sanmaneric/PedalSynth/Diagrams/chorusbreadboard.rev0.jpg

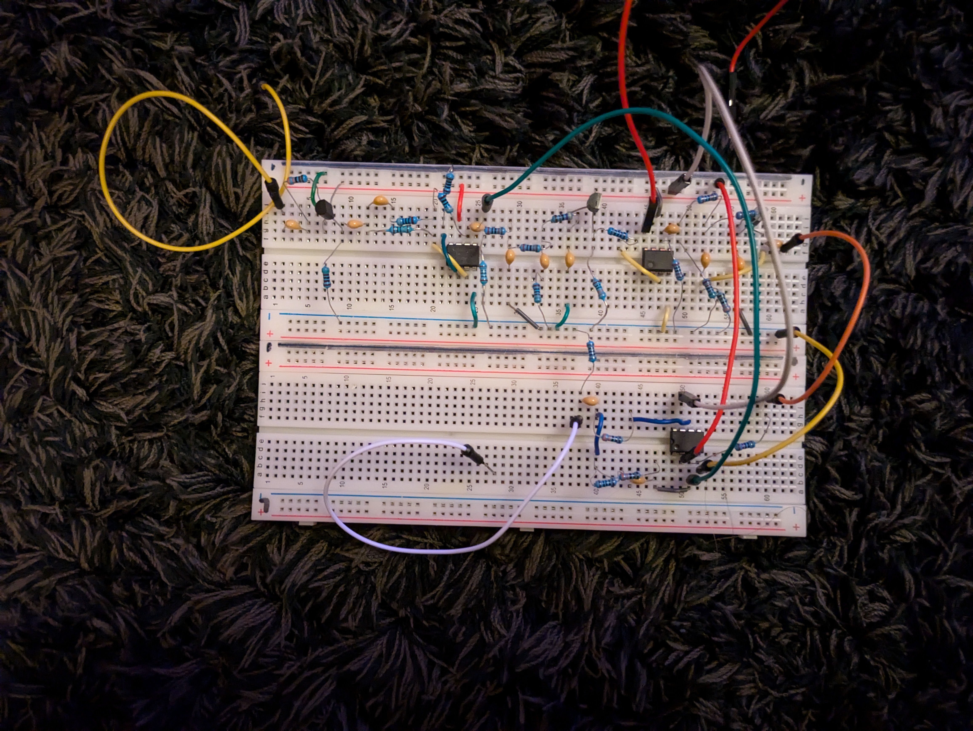
Diagrams/chorusbreadboard.rev0.jpg
