sanmaneric/PedalSynth/Diagrams/Level 0 Diagram.drawio-rev0.png

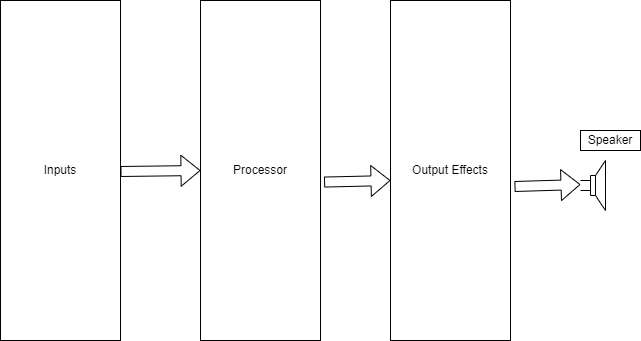
Diagrams/Level 0 Diagram.drawio-rev0.png
