sanmaneric/PedalSynth/Diagrams/Level 1 Diagram.drawio-rev1.png

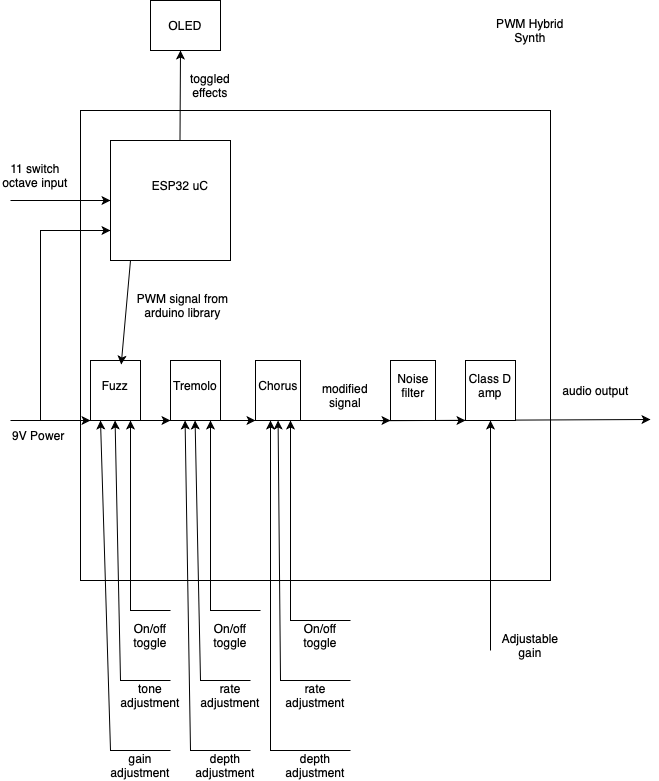
Diagrams/Level 1 Diagram.drawio-rev1.png
