sanmaneric/PedalSynth/Weekly Progress Reports/Progresss Photos/oled-test-14Nov.JPG

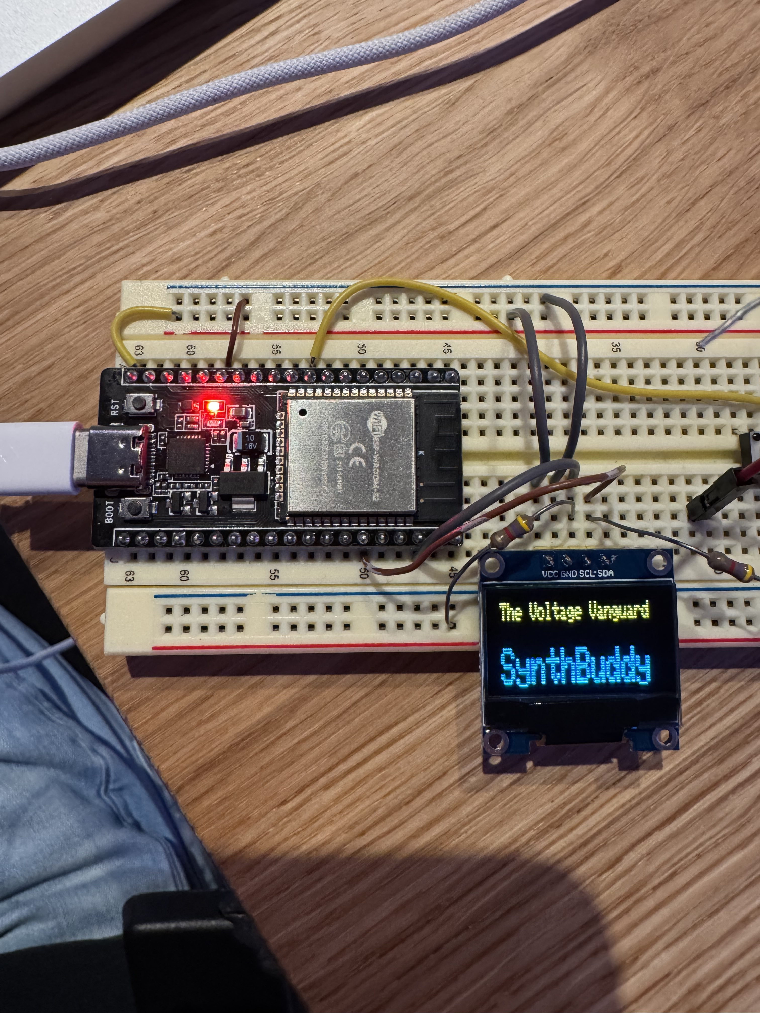
Weekly Progress Reports/Progresss Photos/oled-test-14Nov.JPG
