sanmaneric/PedalSynth/Electrical Design/Docs/Combined Design Package/PedalSynth-Pkg-7Nov.pdf

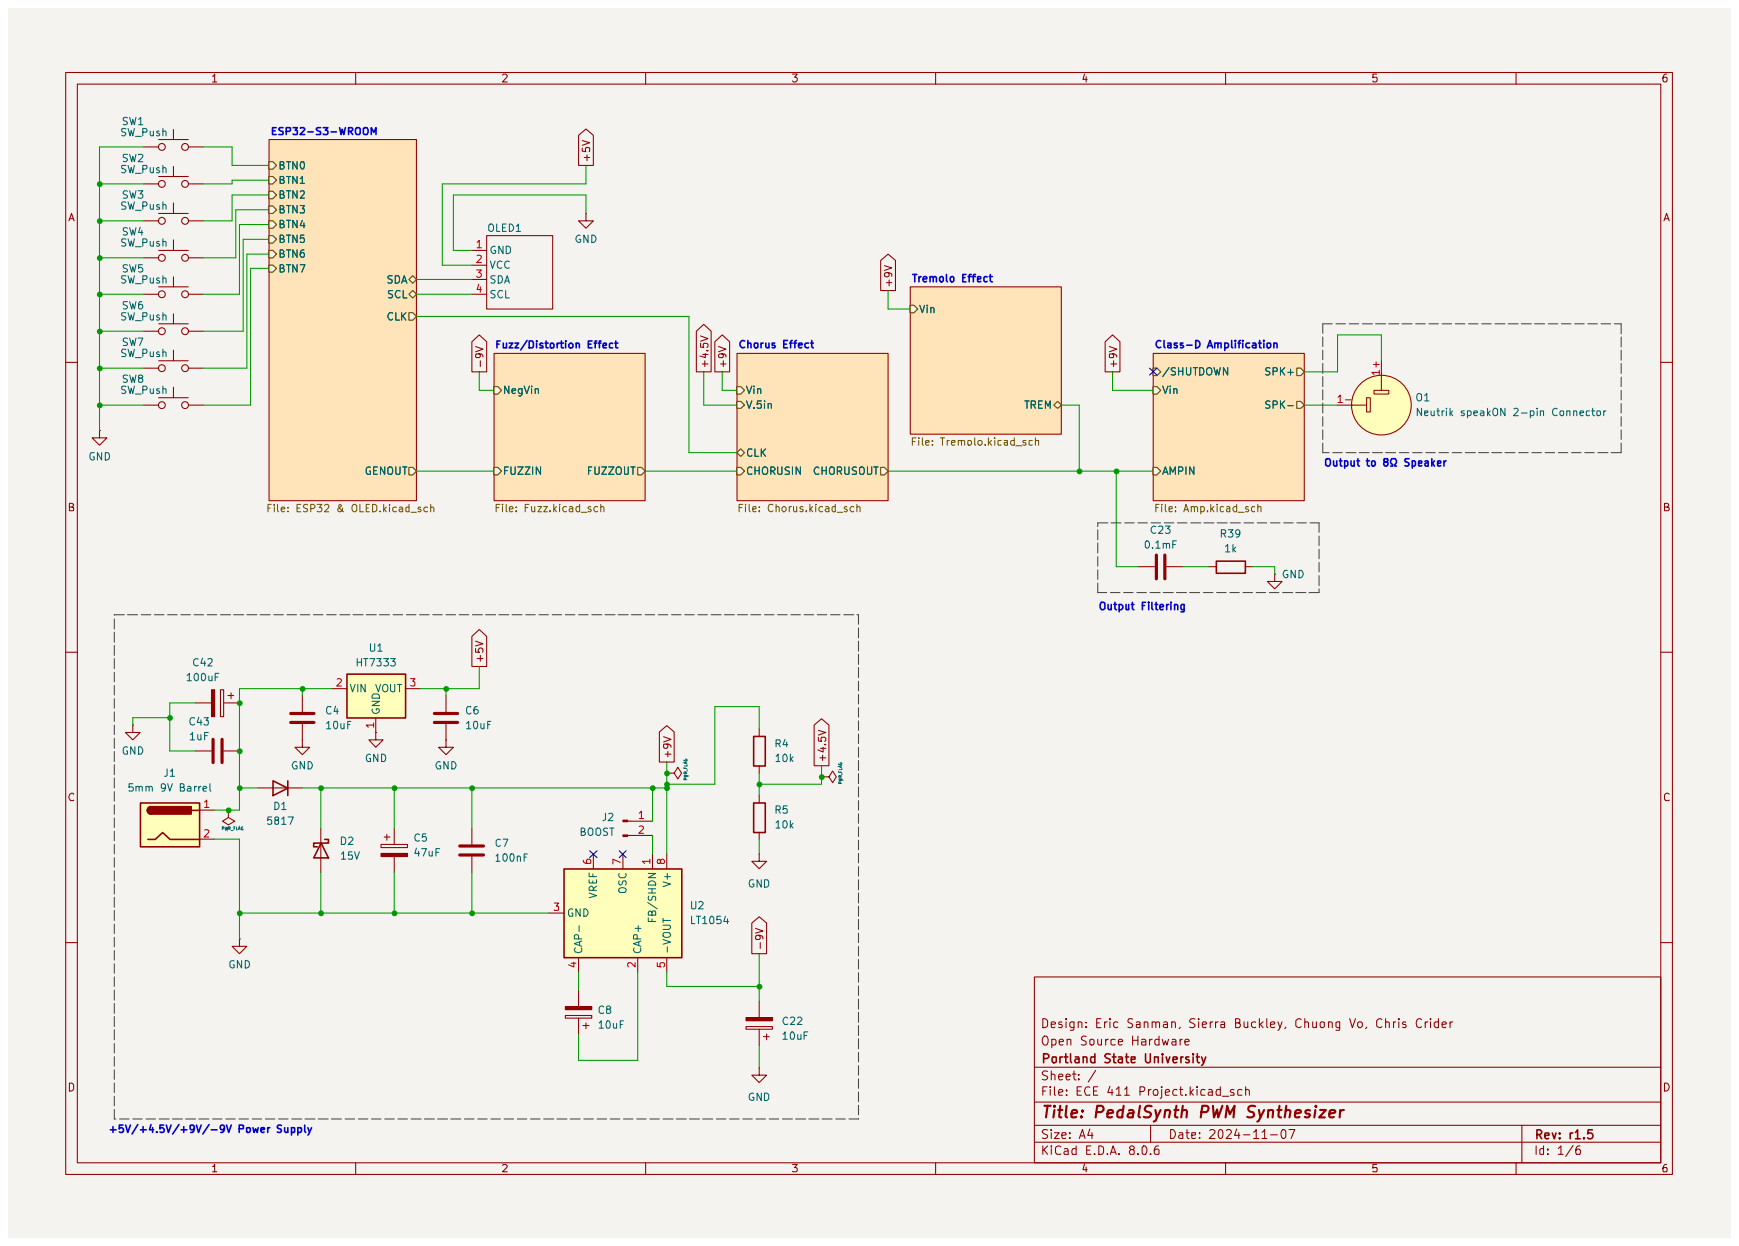
[picture p41: page 1]

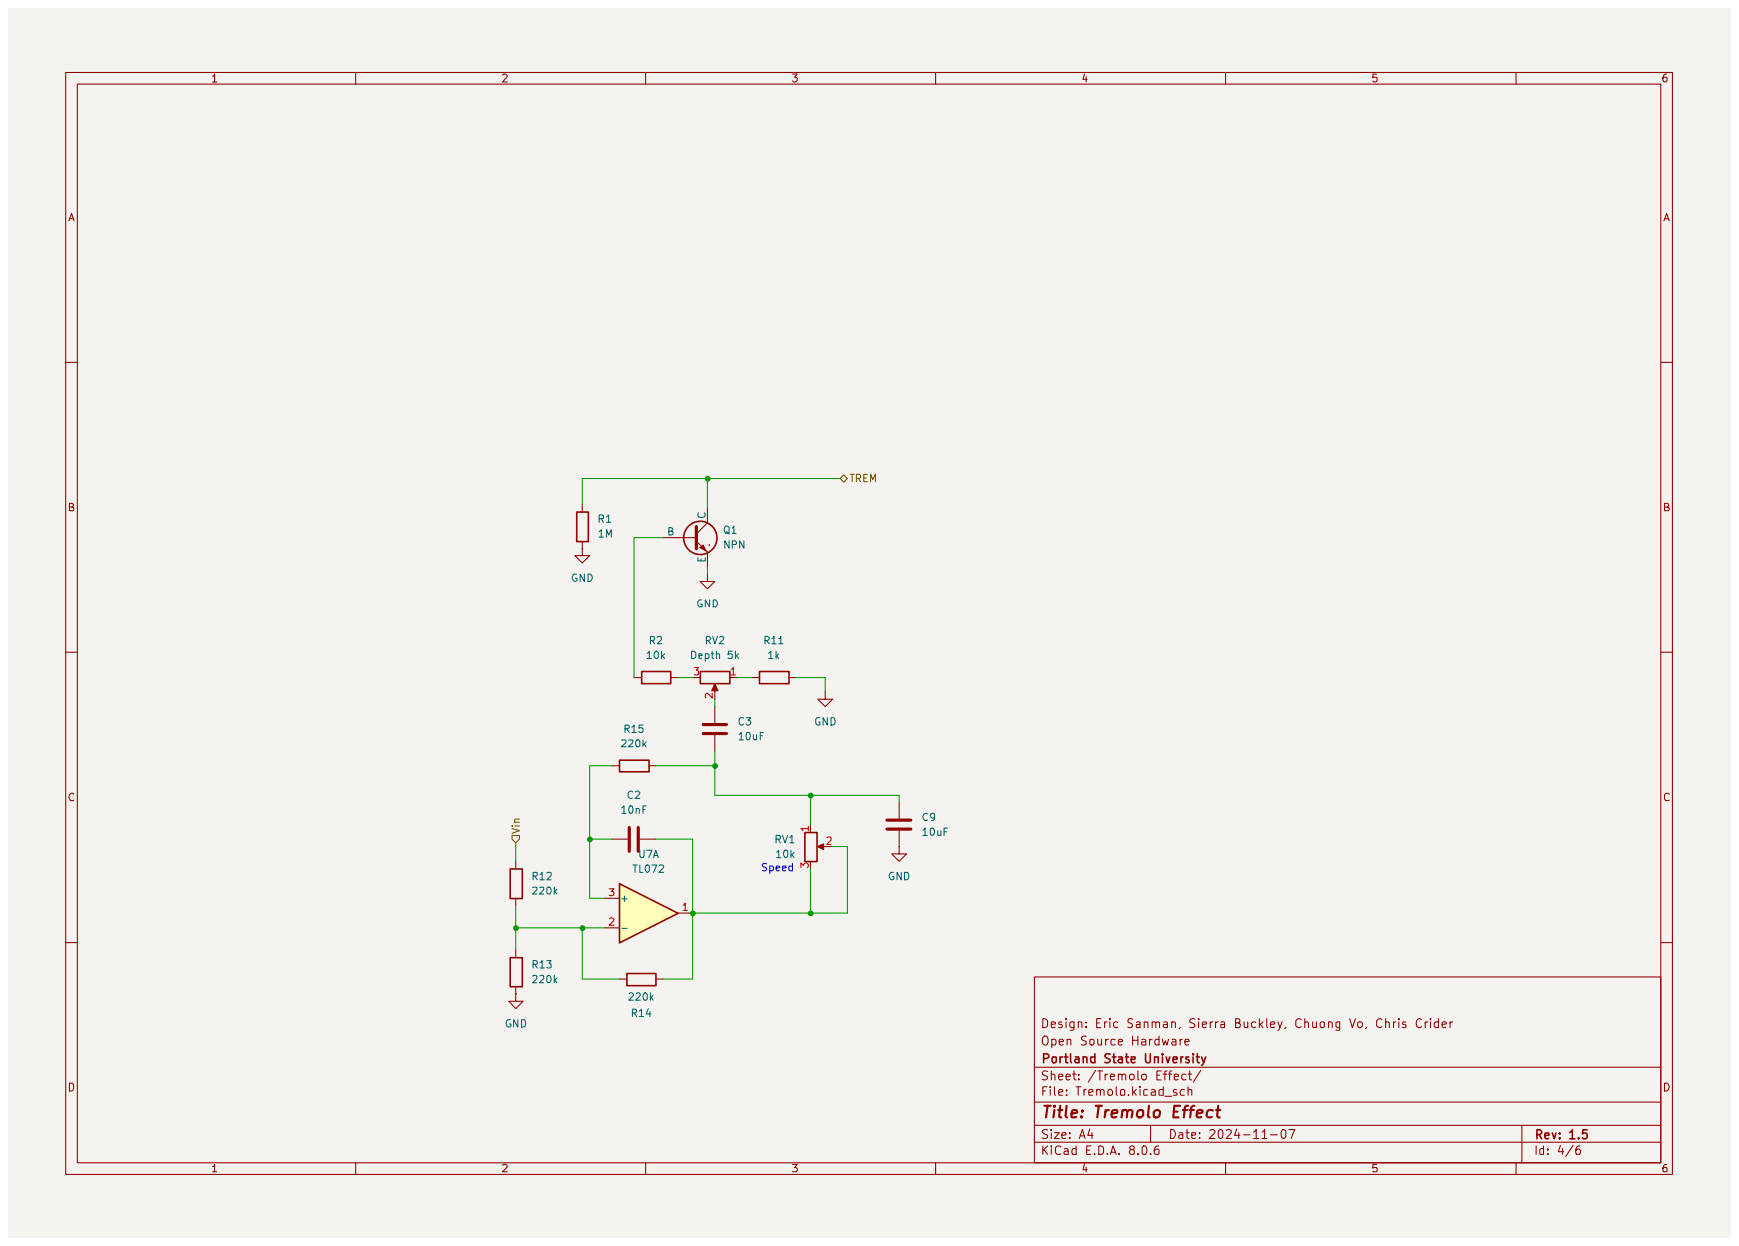
[picture p42: page 2]

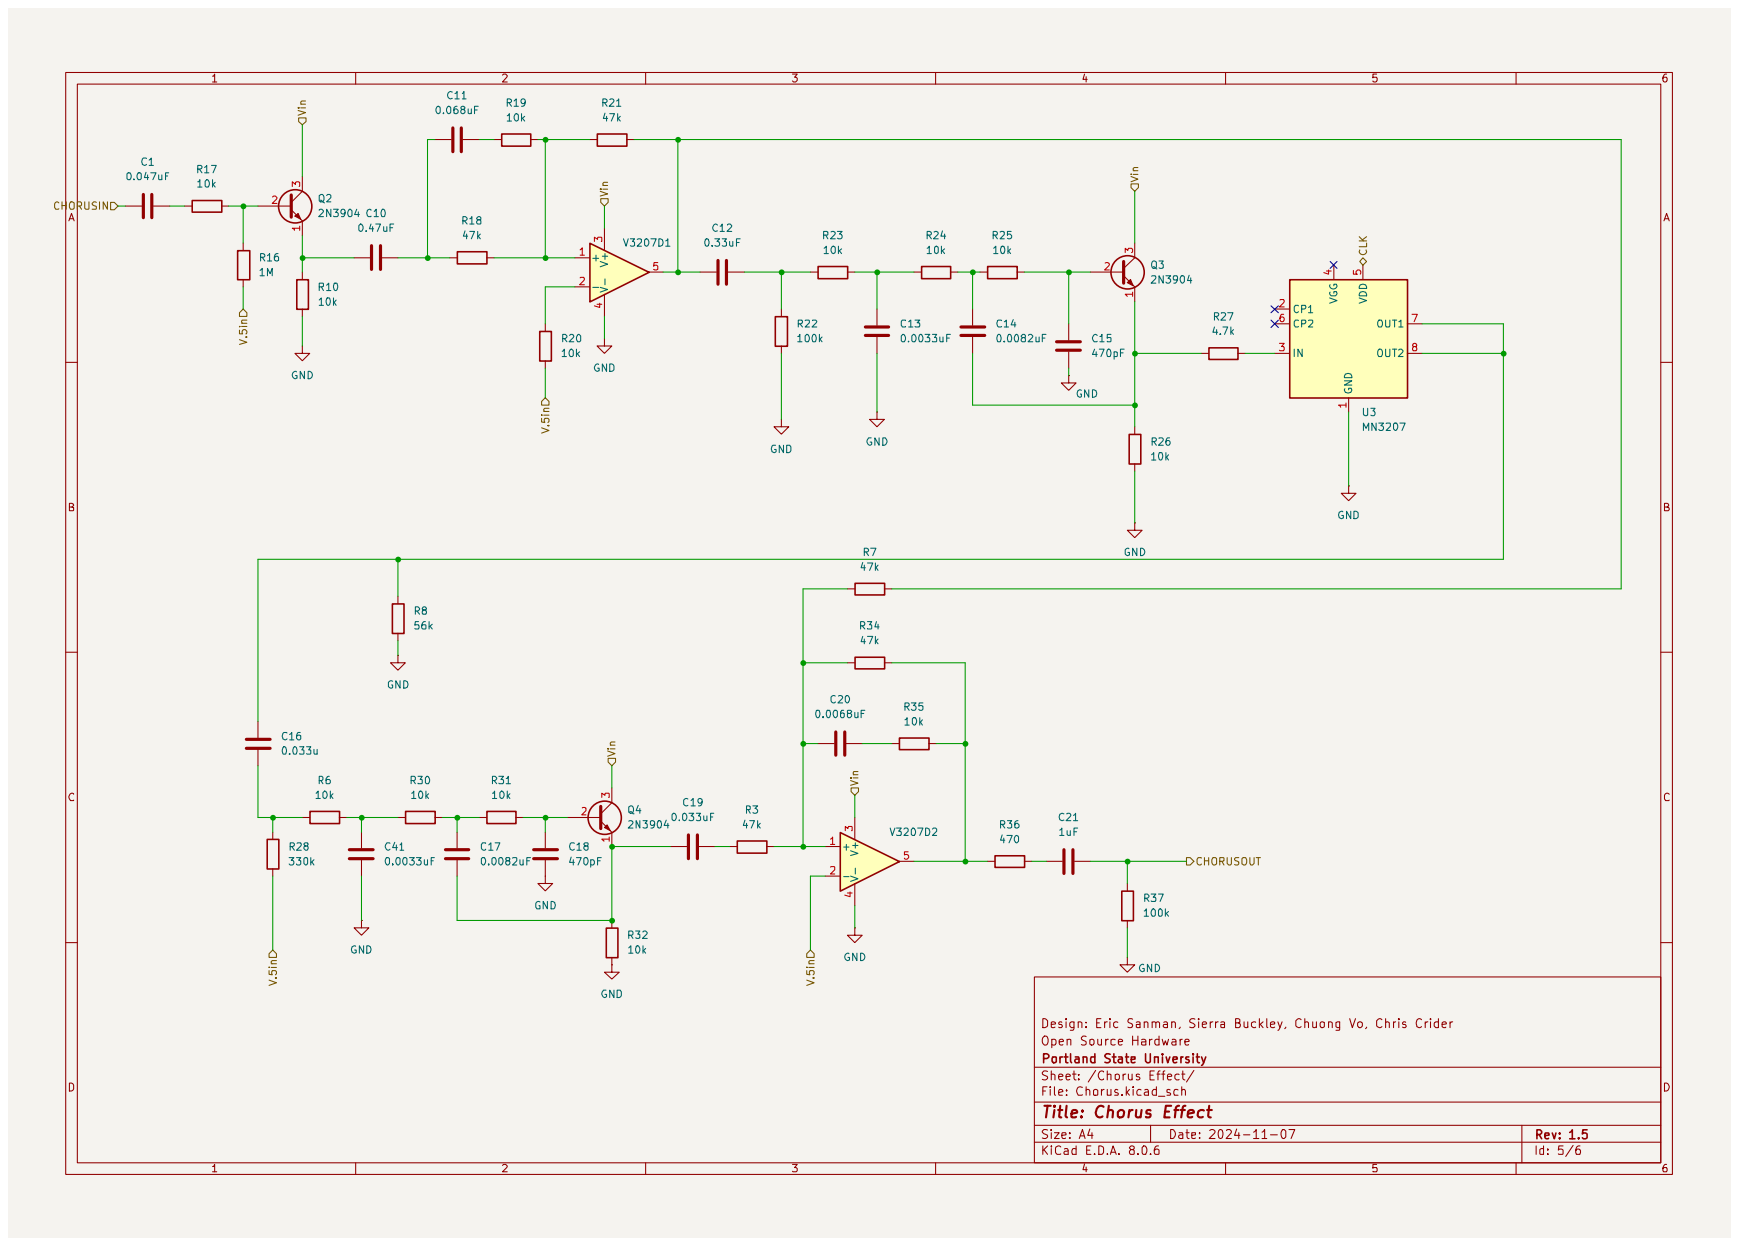
[picture p43: page 3]

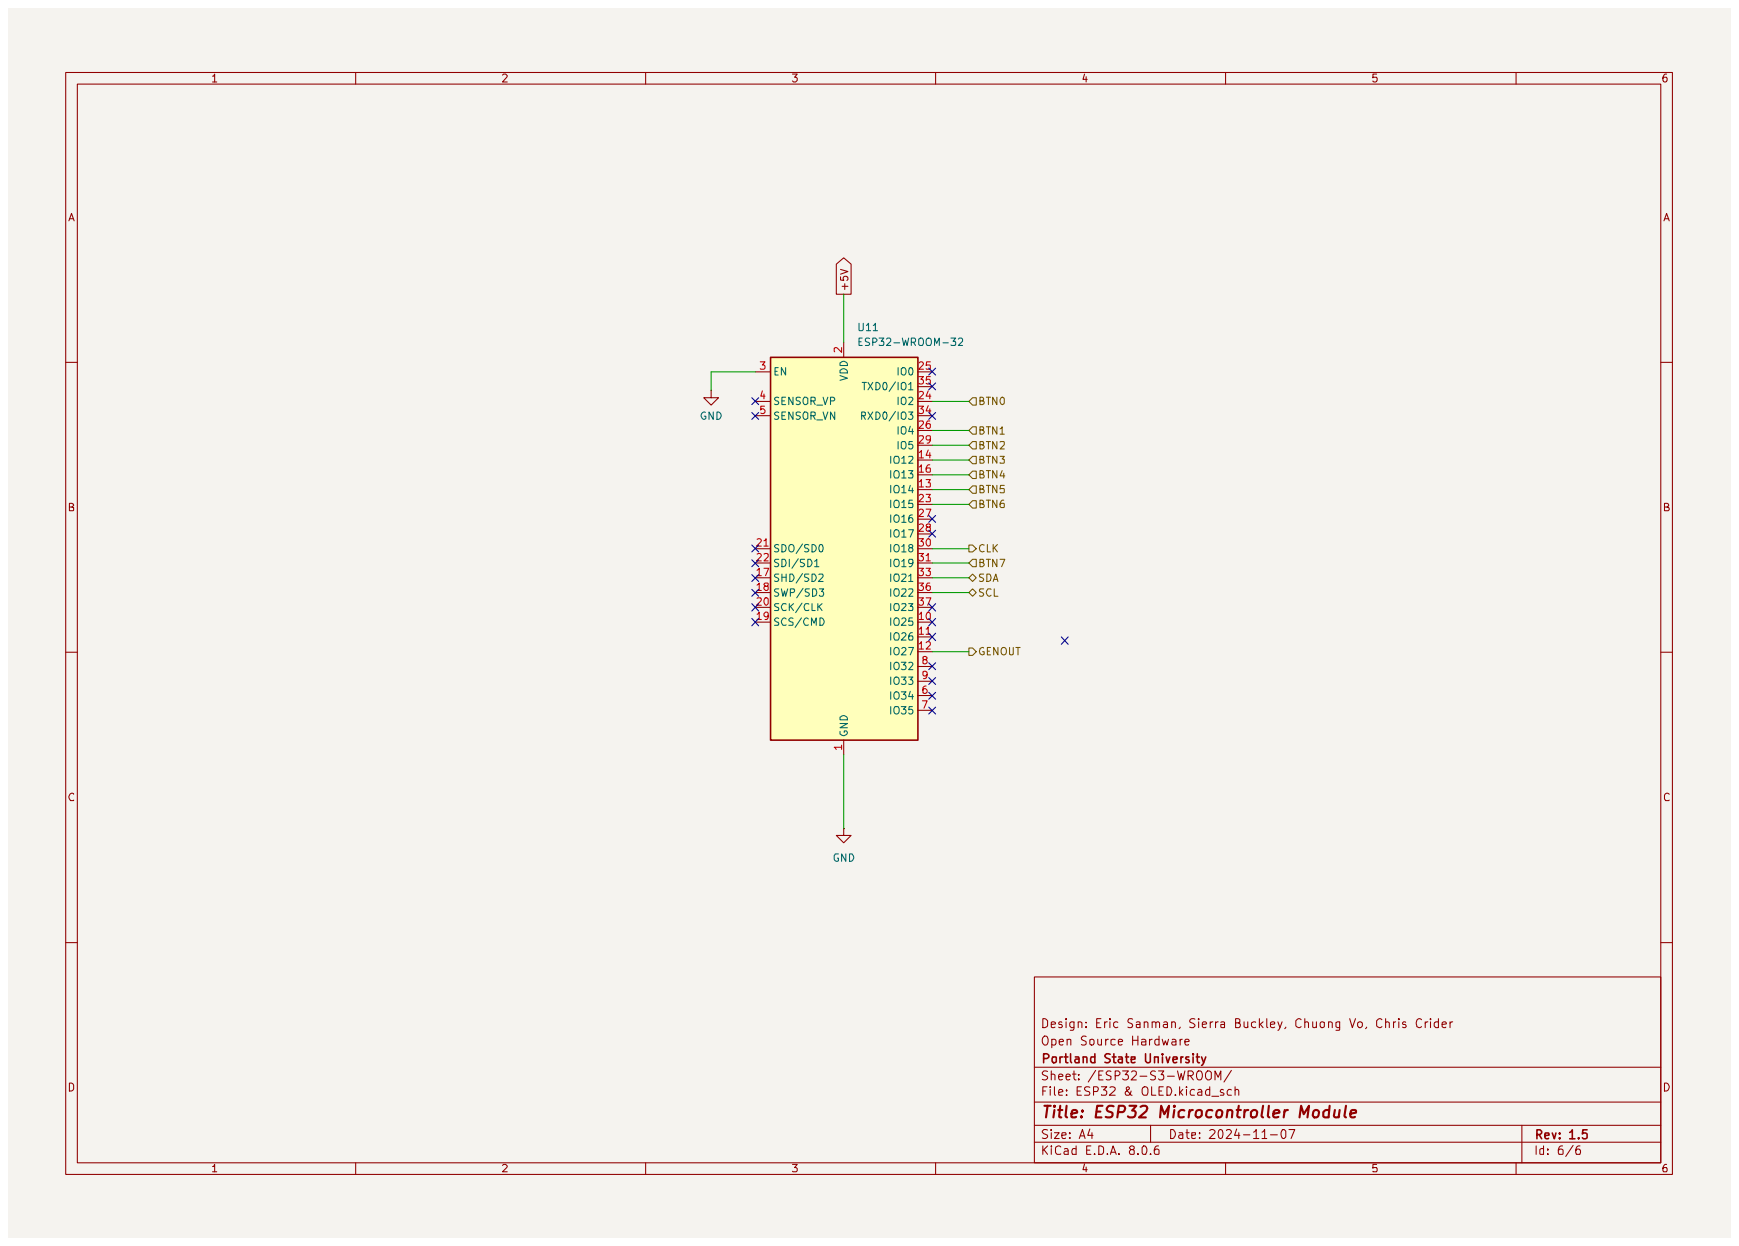
[picture p44: page 4]

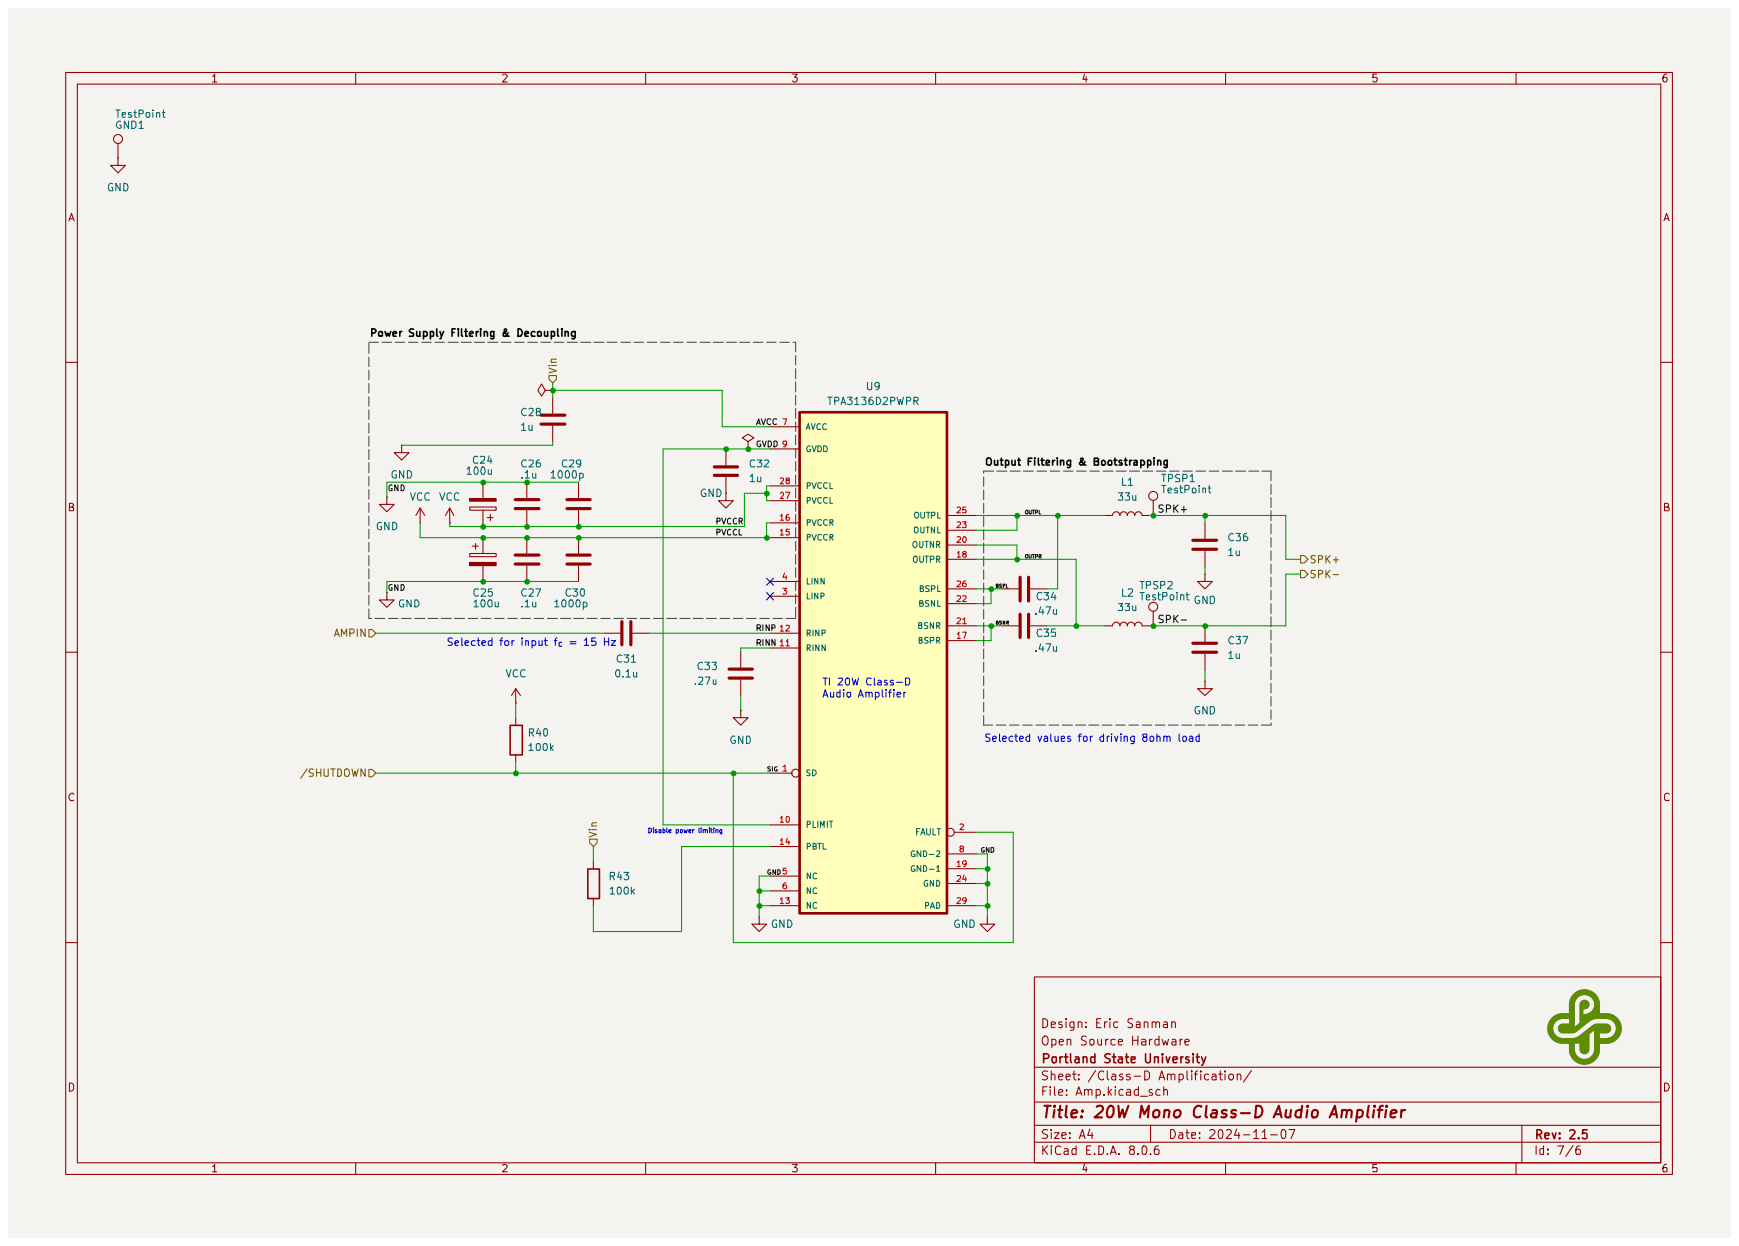
[picture p45: page 5]

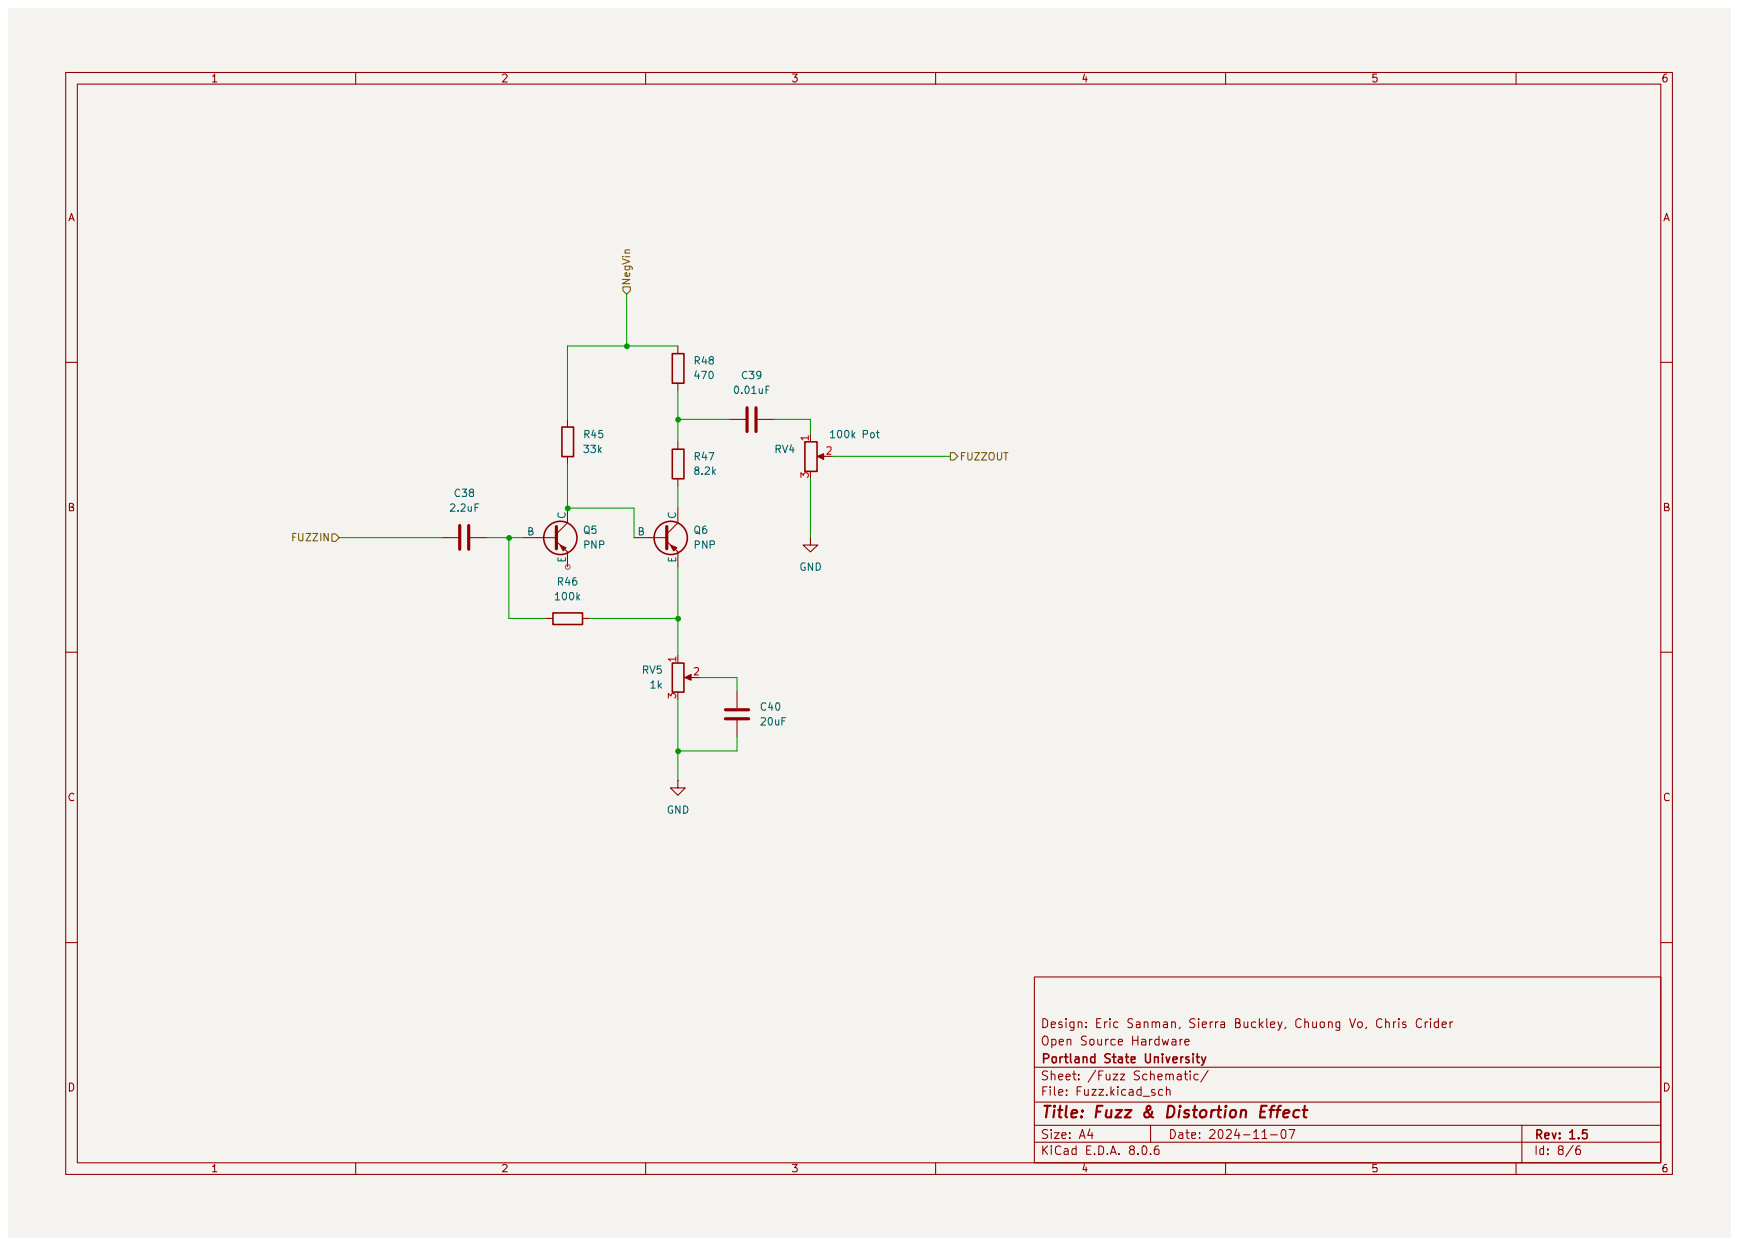
[picture p46: page 6]

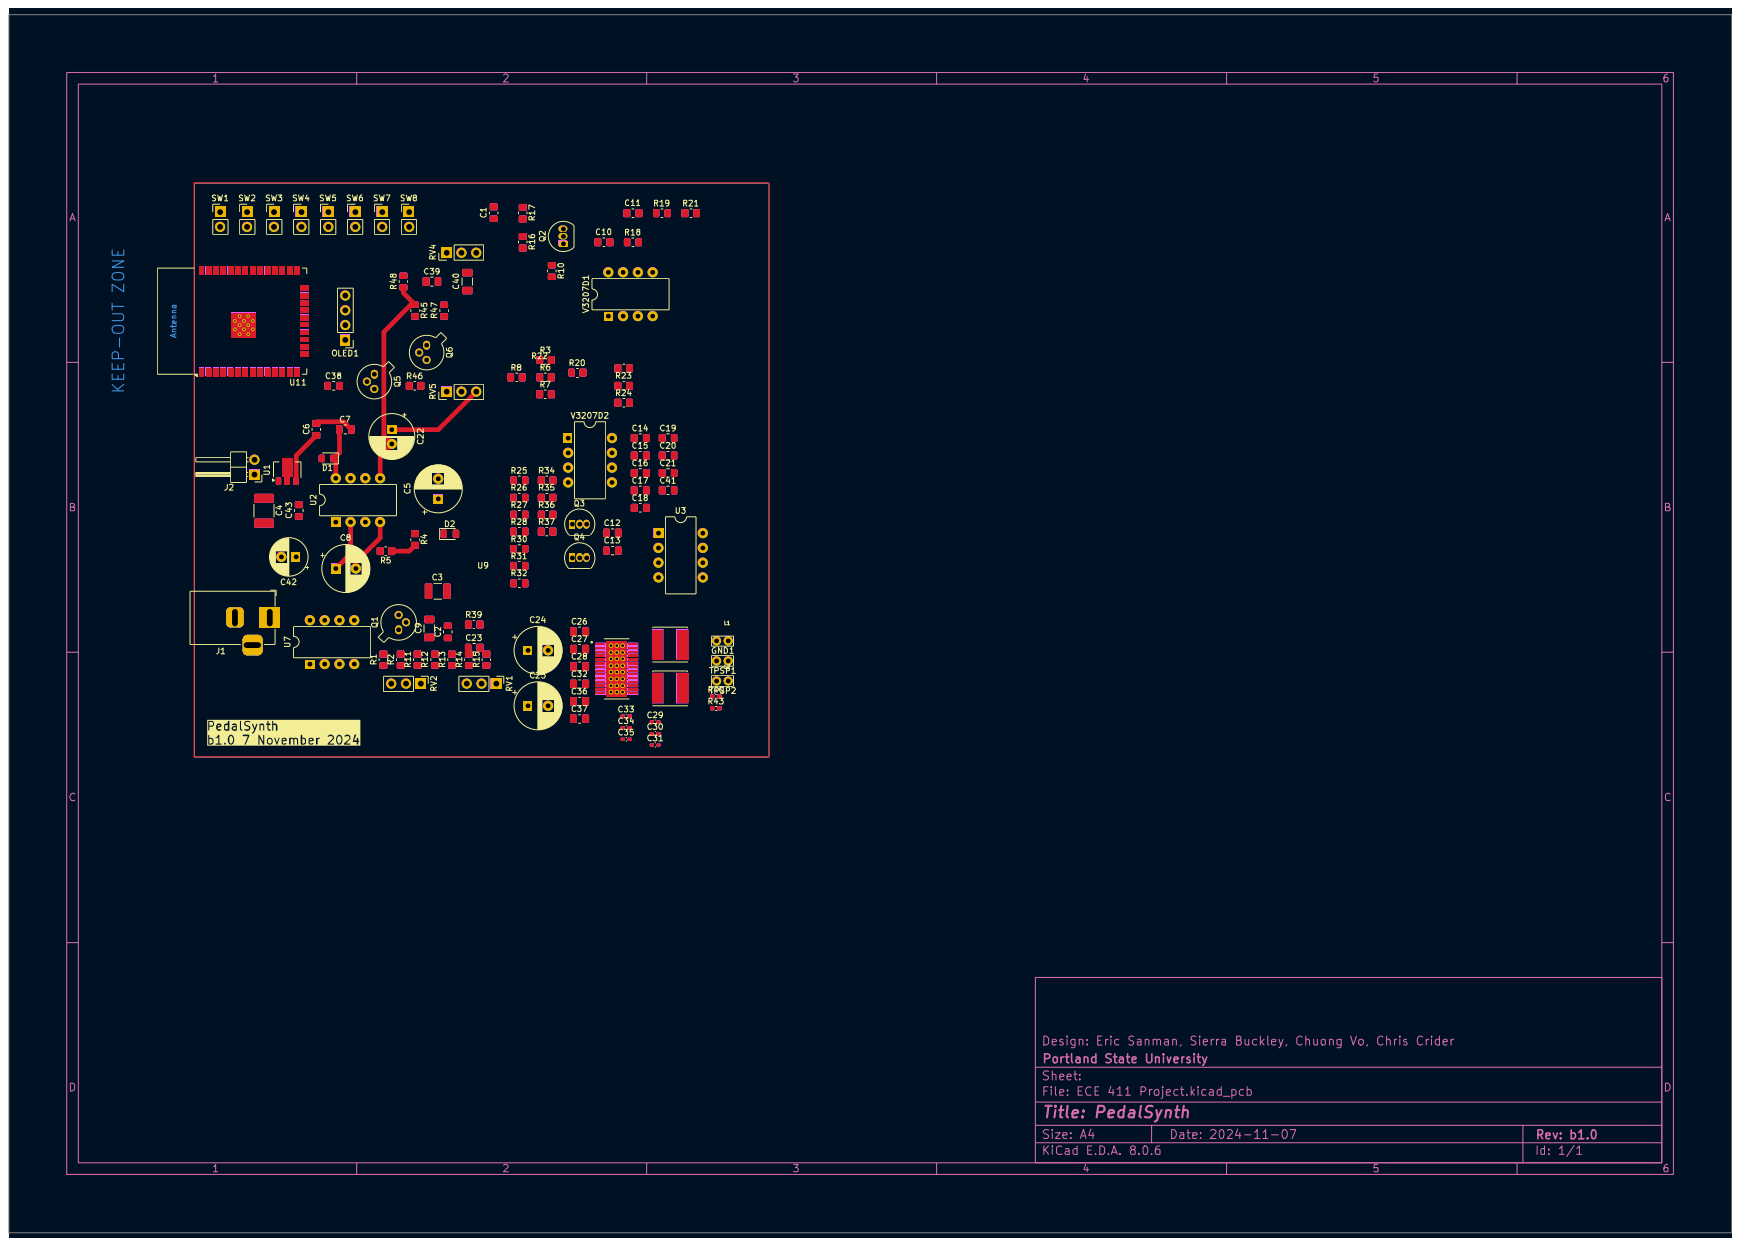
[picture p47: page 7]
